arafferty10/safeCracking/img/IMG_1752.jpg

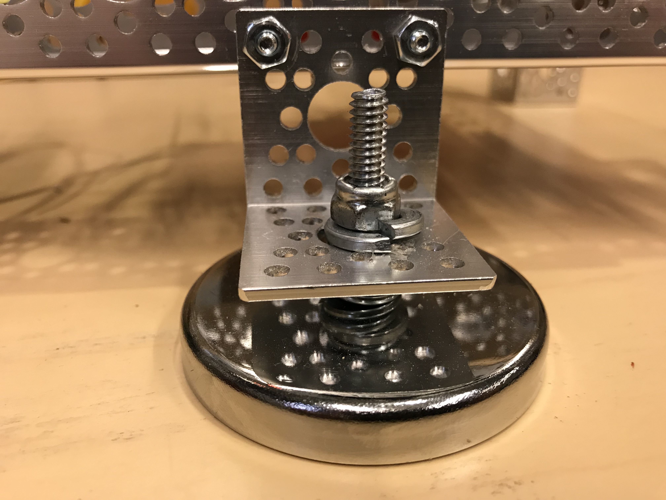
img/IMG_1752.jpg
