arafferty10/safeCracking/img/IMG_1755.jpg

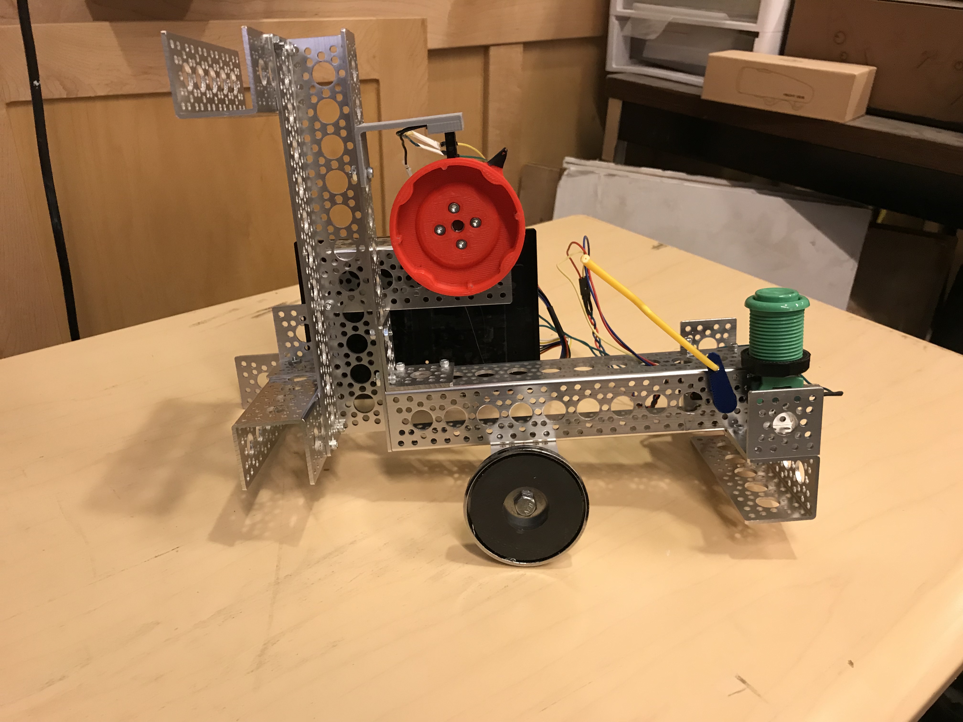
img/IMG_1755.jpg
